jlcjak/astra_piNas/docs/images/render-bottom.png

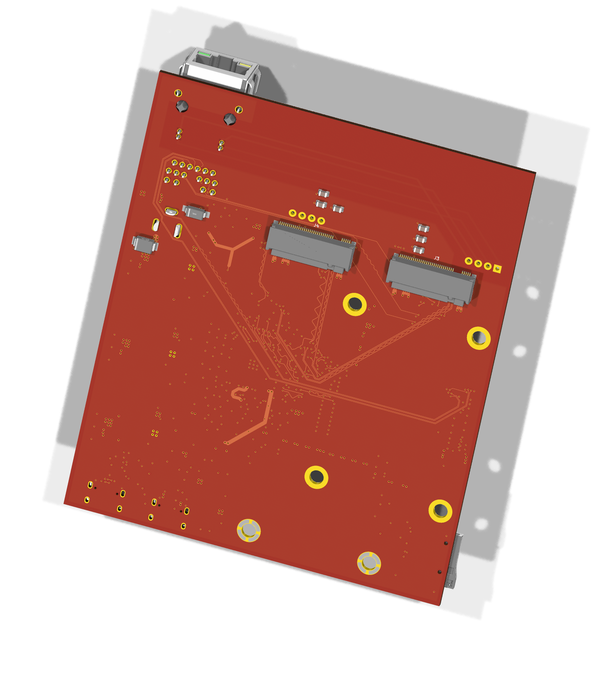
docs/images/render-bottom.png
