jlcjak/astra_piNas/docs/images/render-top.png

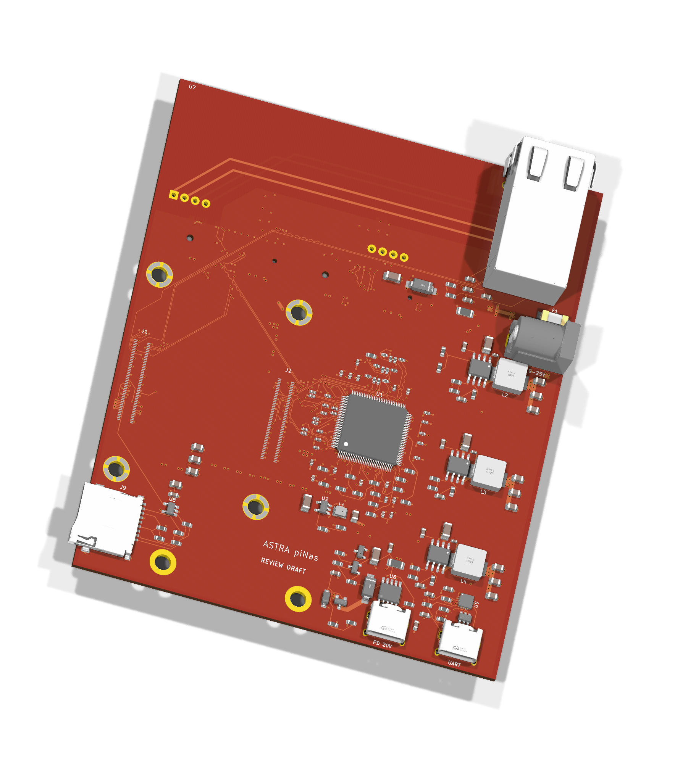
docs/images/render-top.png
