jlcjak/astra_piNas/docs/inputs_review.png

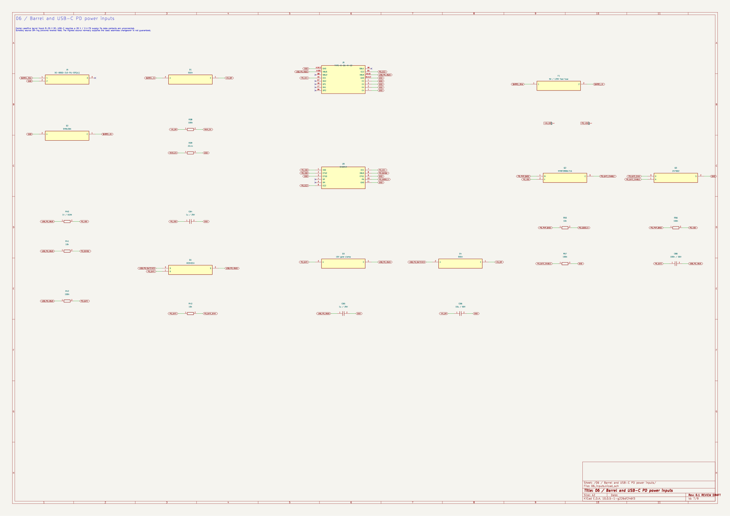
docs/inputs_review.png
