jlcjak/astra_piNas/docs/pcie_review.png

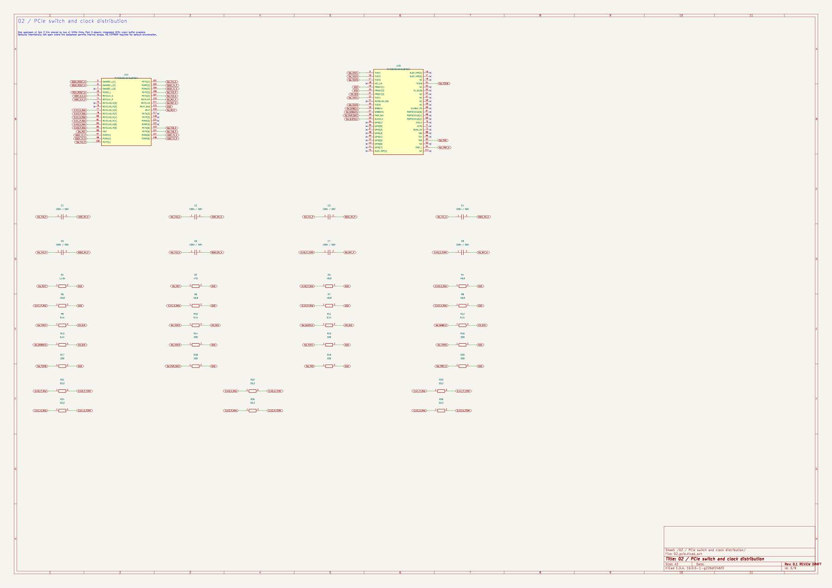
docs/pcie_review.png
