jlcjak/astra_piNas/sources/barrel_reference.png

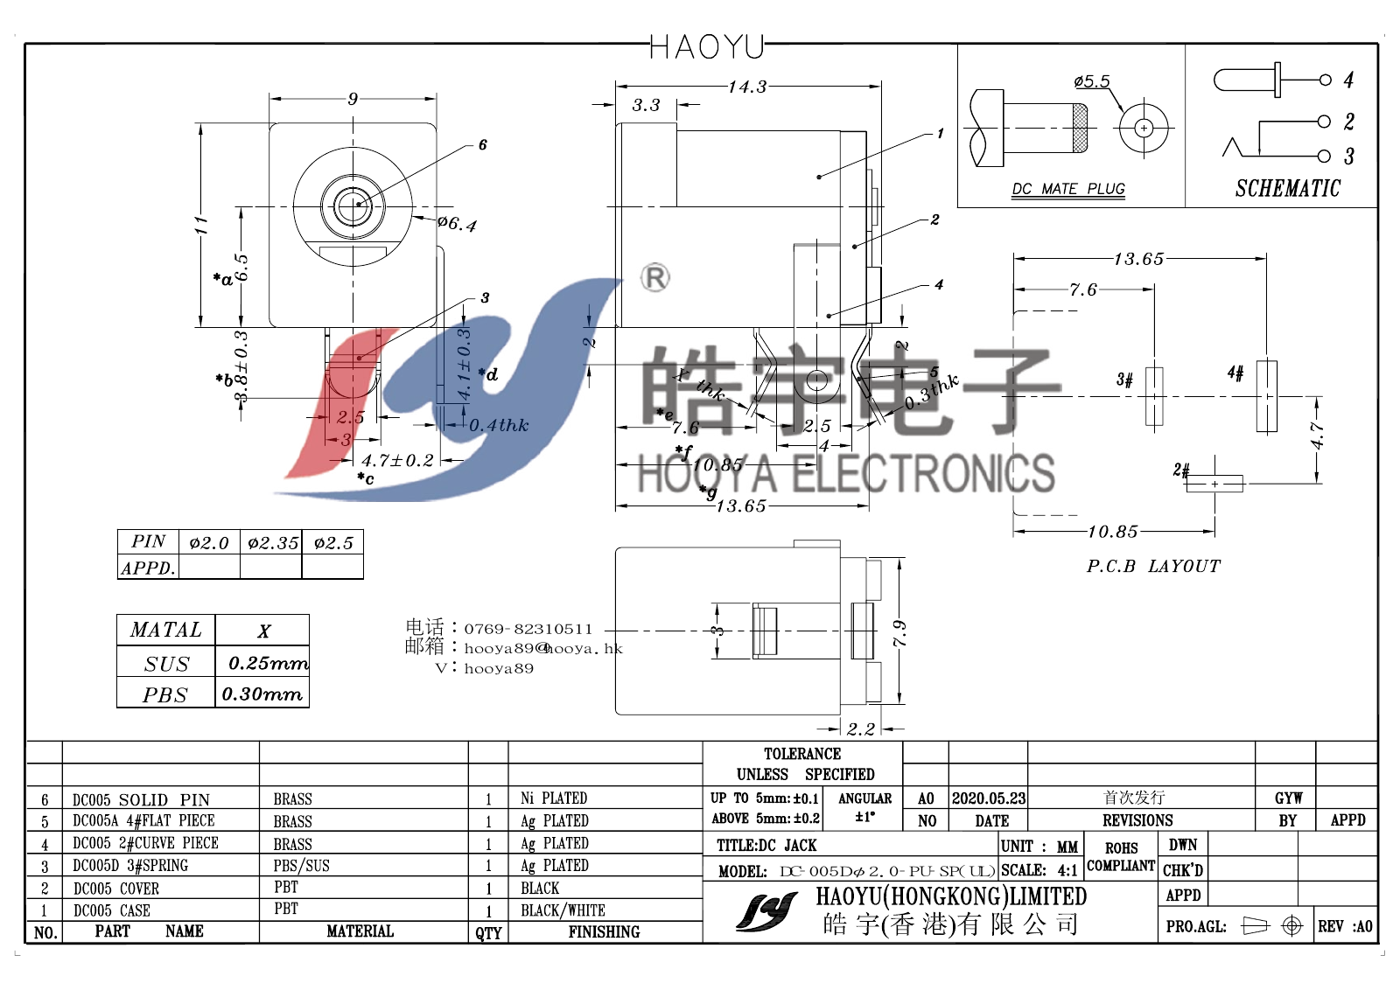
sources/barrel_reference.png
