jlcjak/astra_piNas/sources/cm_land.png

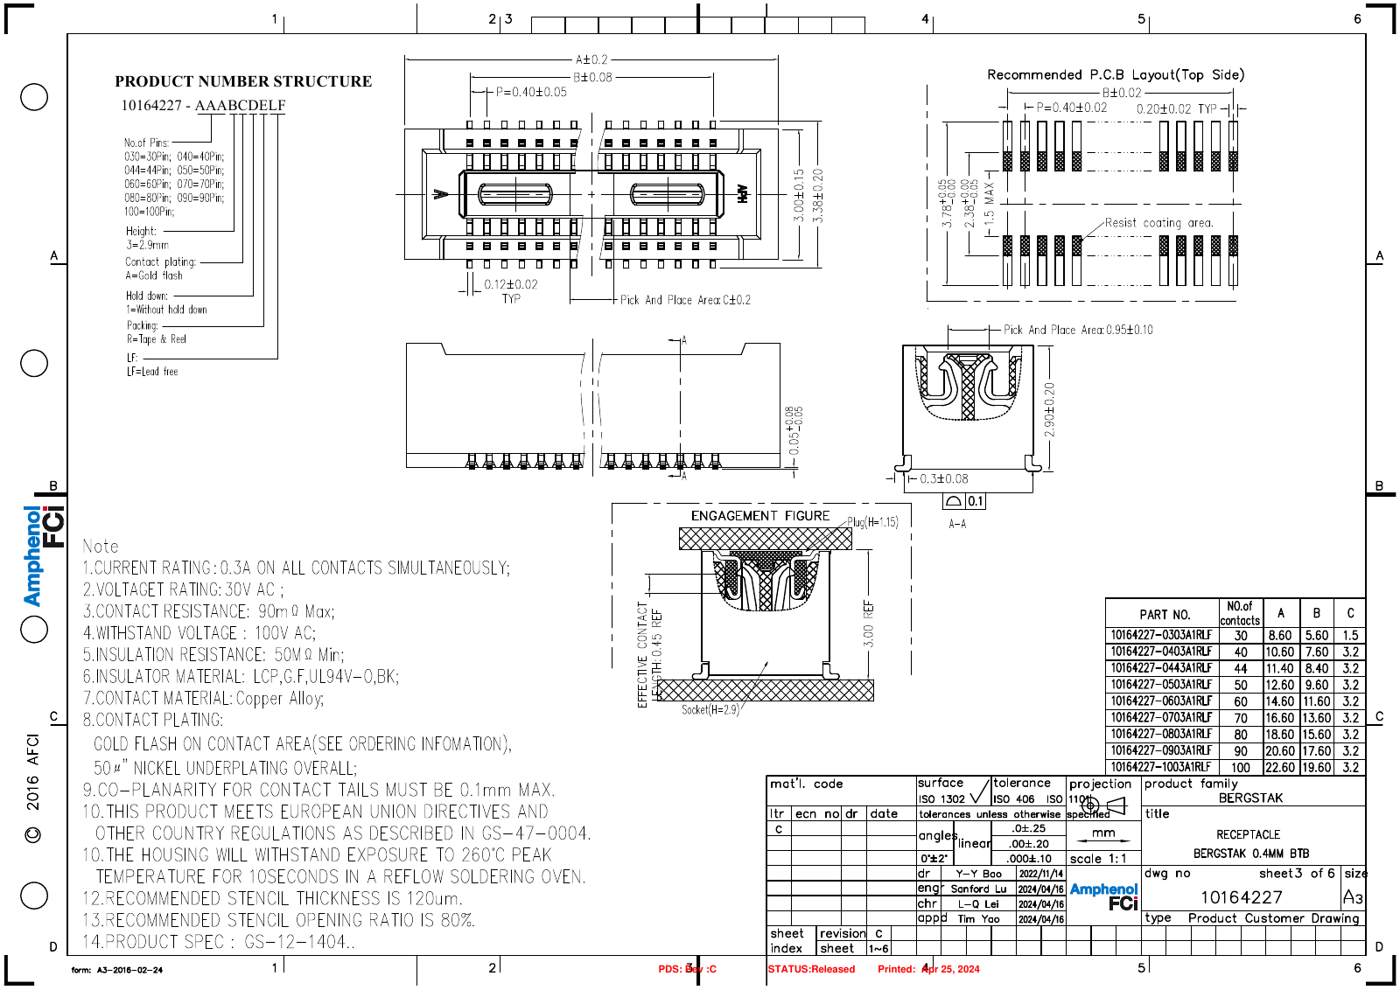
sources/cm_land.png
