jlcjak/astra_piNas/sources/m2_body.png

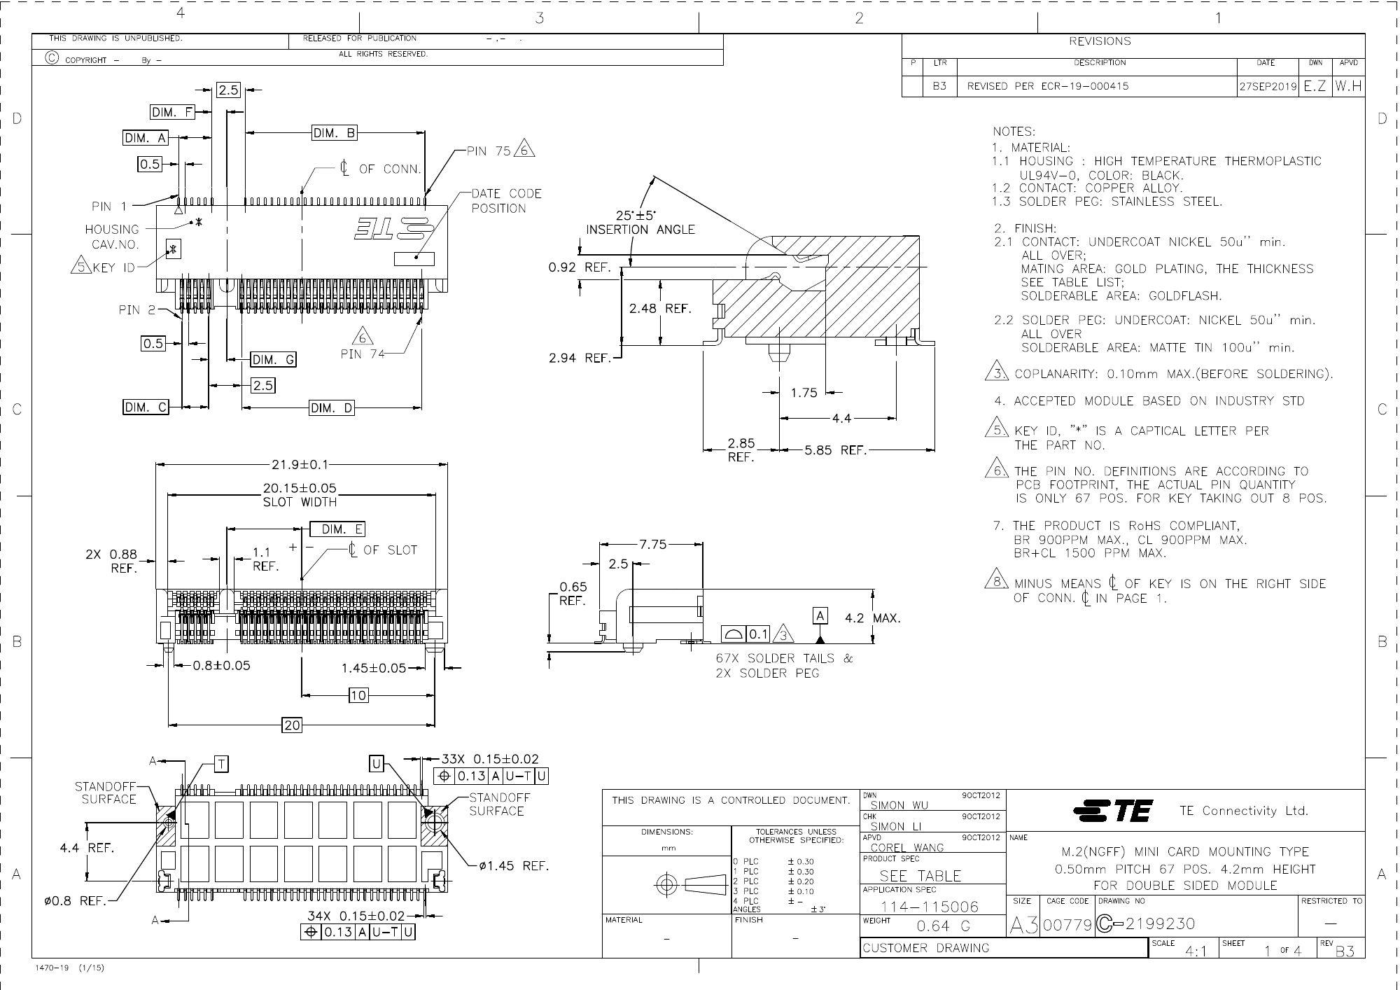
sources/m2_body.png
