jlcjak/astra_piNas/sources/m2_drawing.png

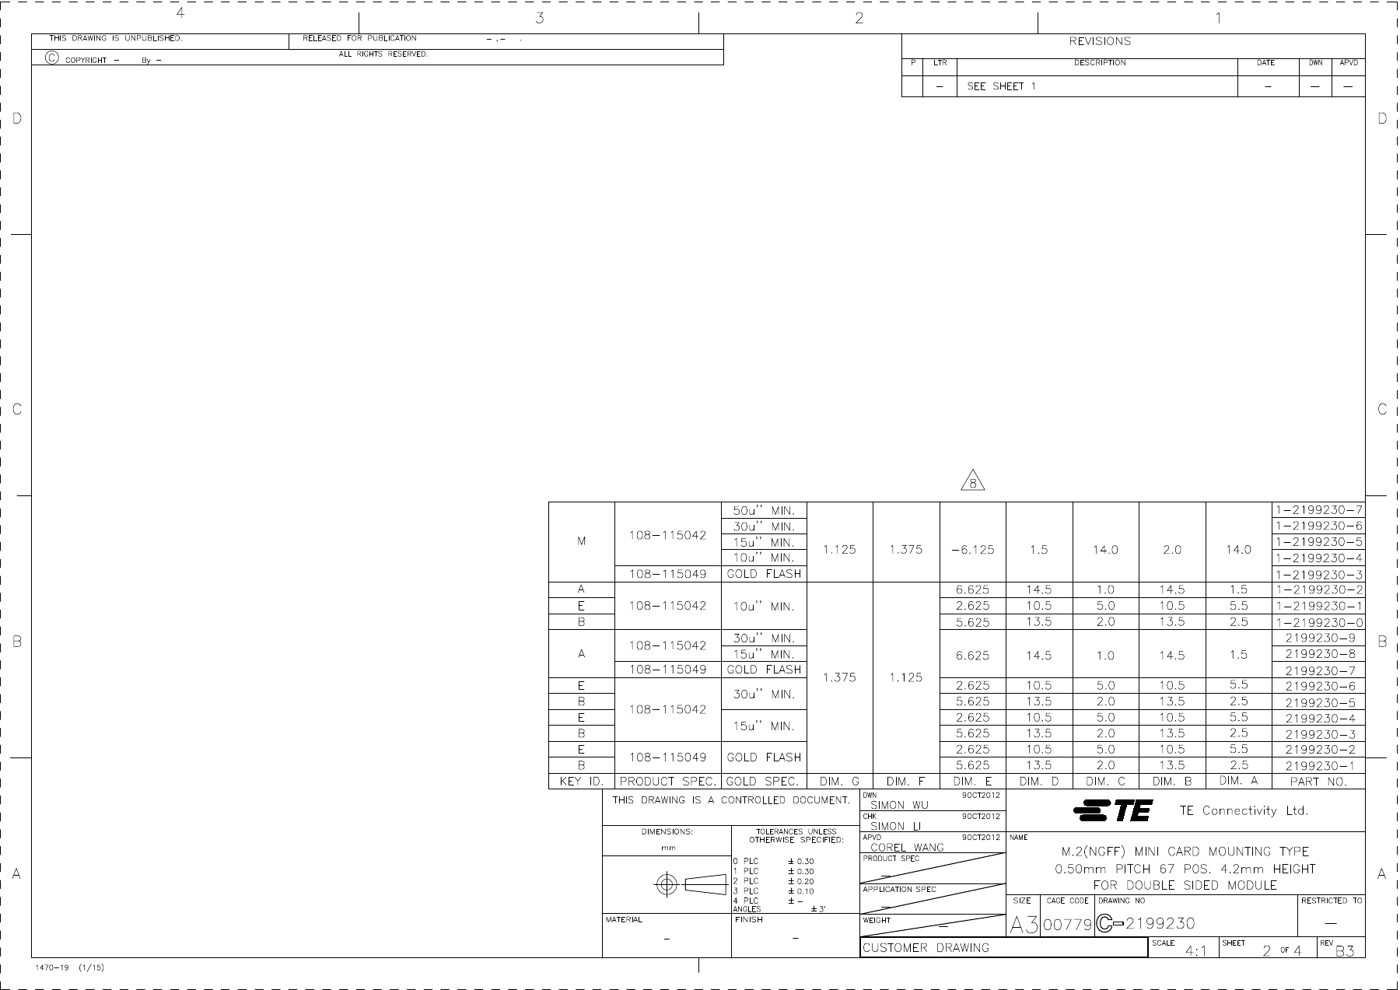
sources/m2_drawing.png
