jlcjak/astra_piNas/sources/m2_land.png

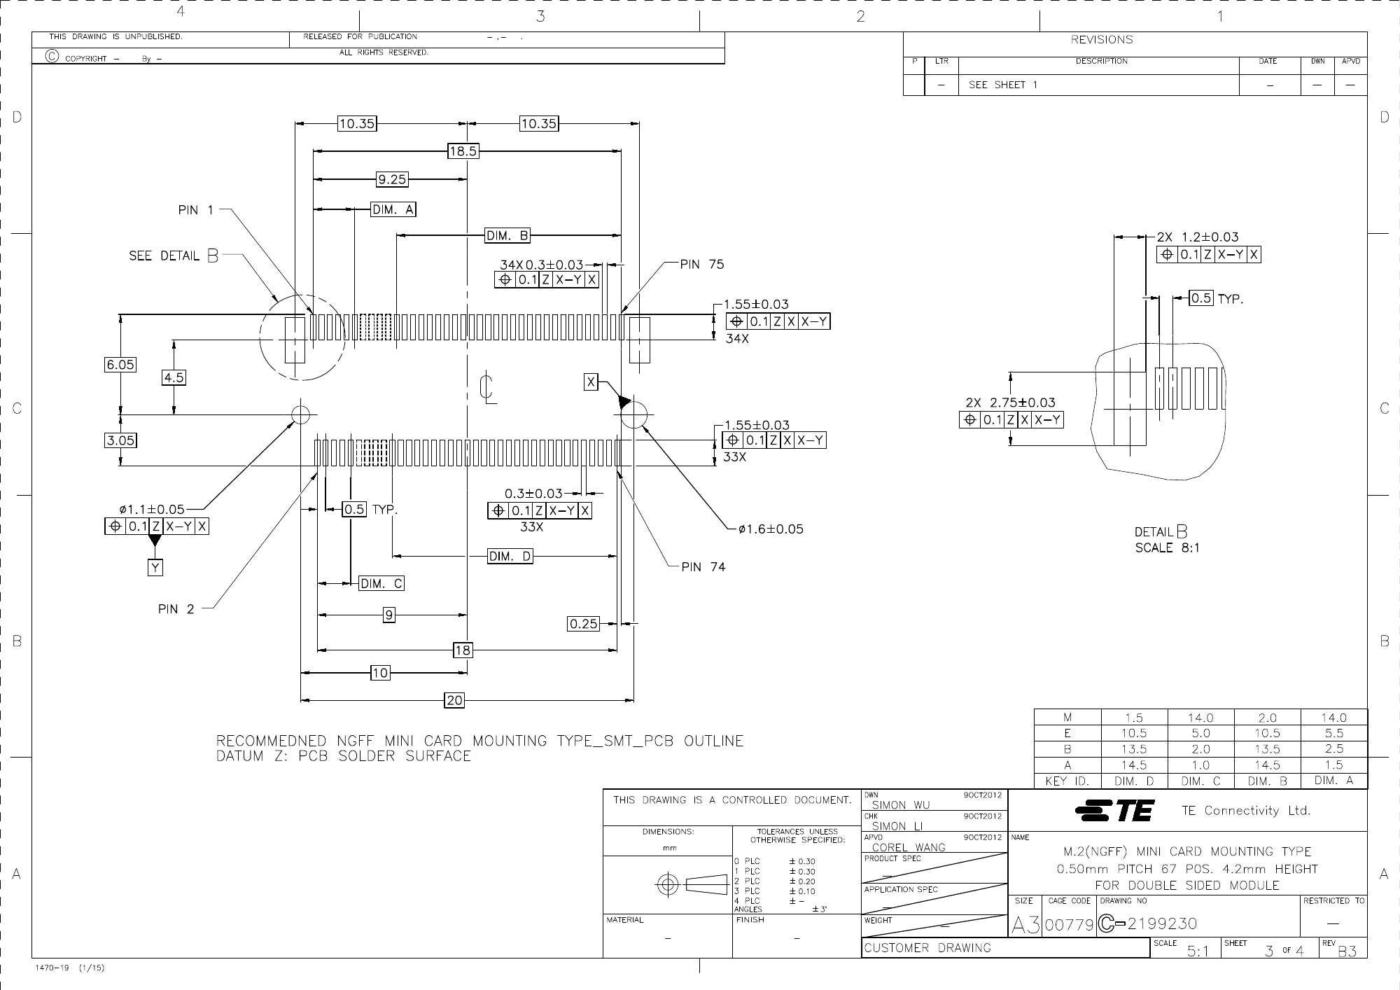
sources/m2_land.png
