jlcjak/astra_piNas/sources/m2_mount.png

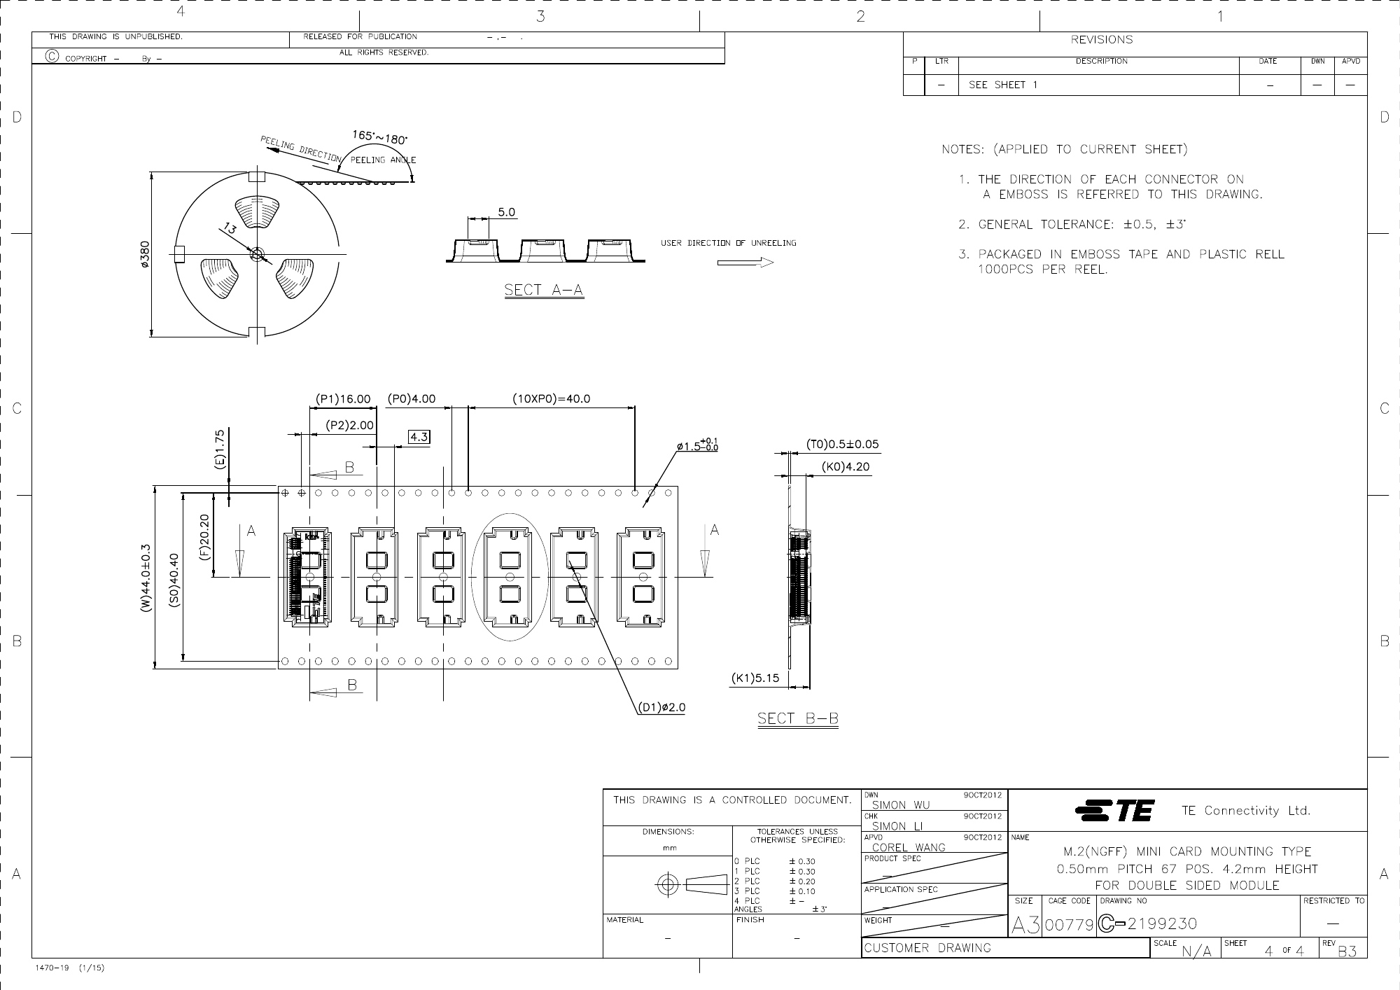
sources/m2_mount.png
