jlcjak/astra_piNas/sources/magjack_circuit.png

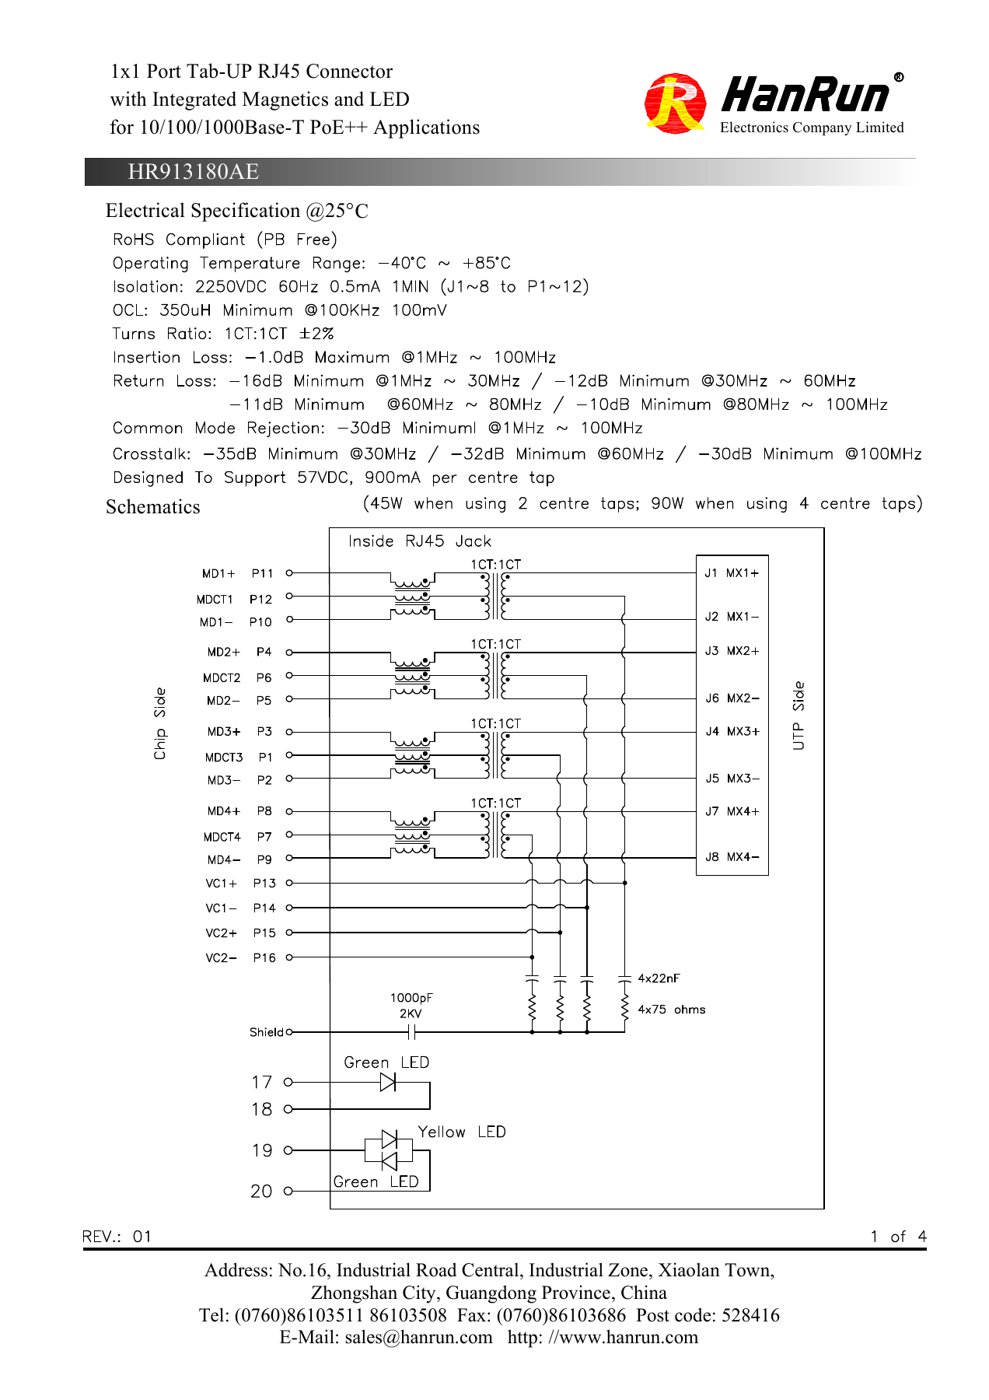
sources/magjack_circuit.png
