jlcjak/astra_piNas/sources/magjack_diagram.png

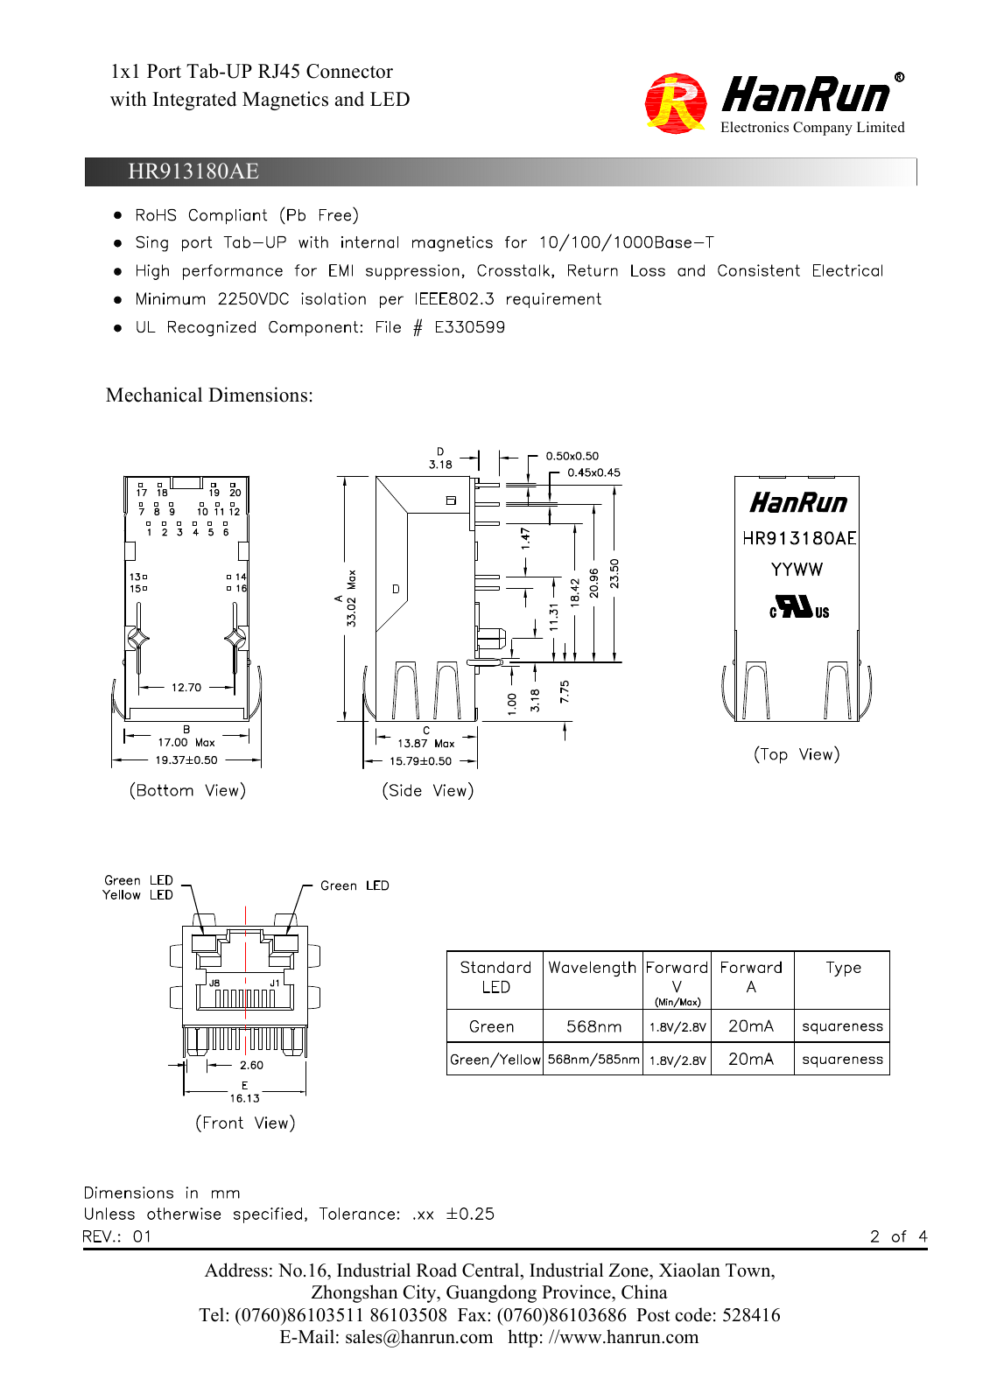
sources/magjack_diagram.png
