jlcjak/astra_piNas/sources/pd_reference.png

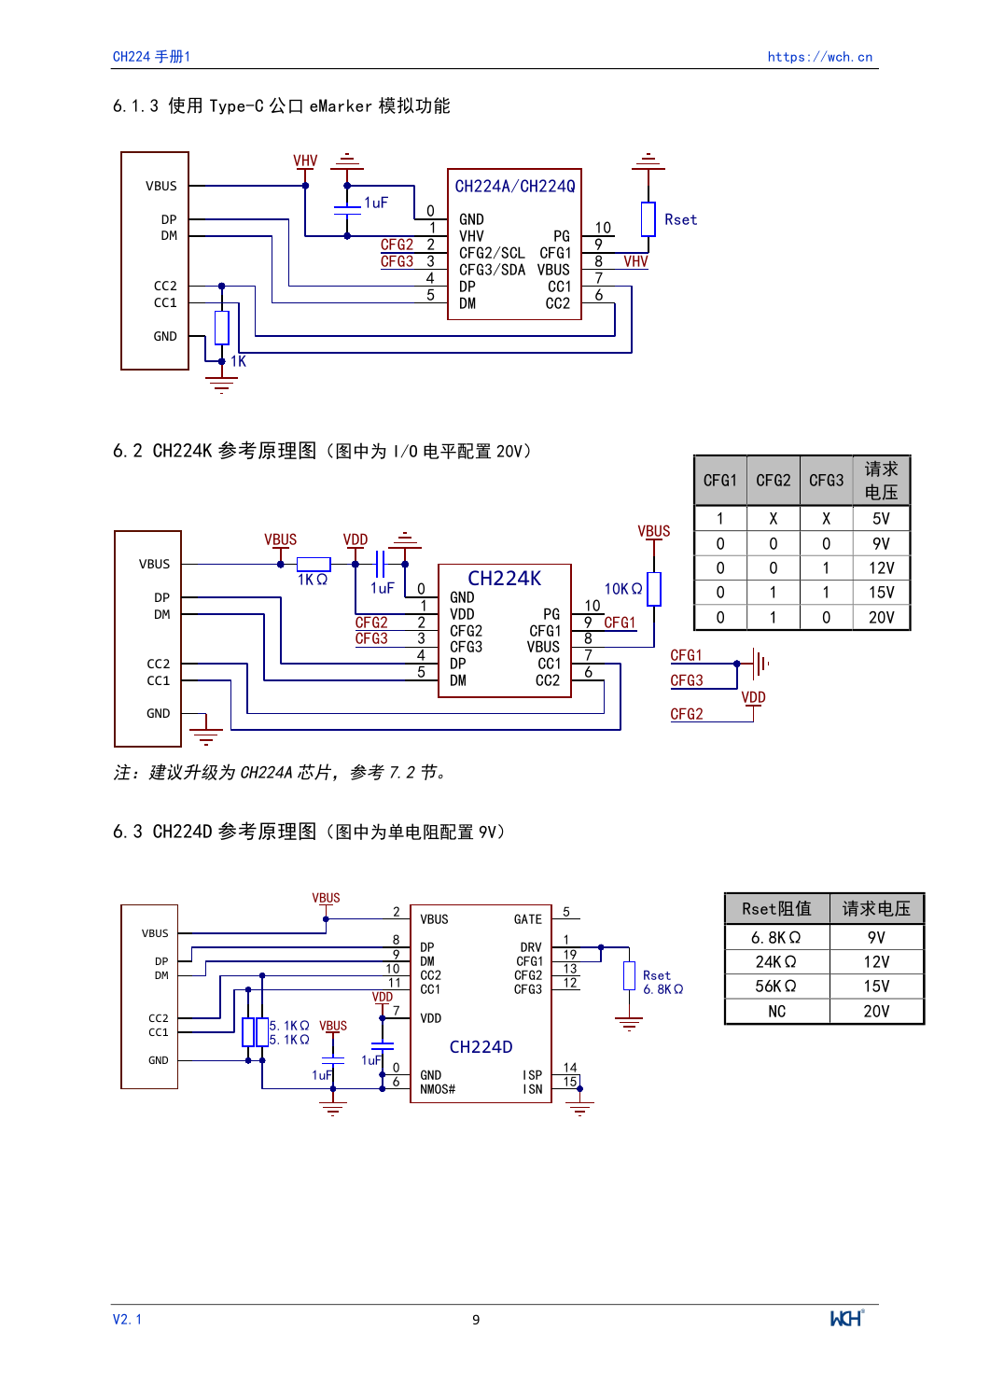
sources/pd_reference.png
