jlcjak/astra_piNas/sources/standoff.png

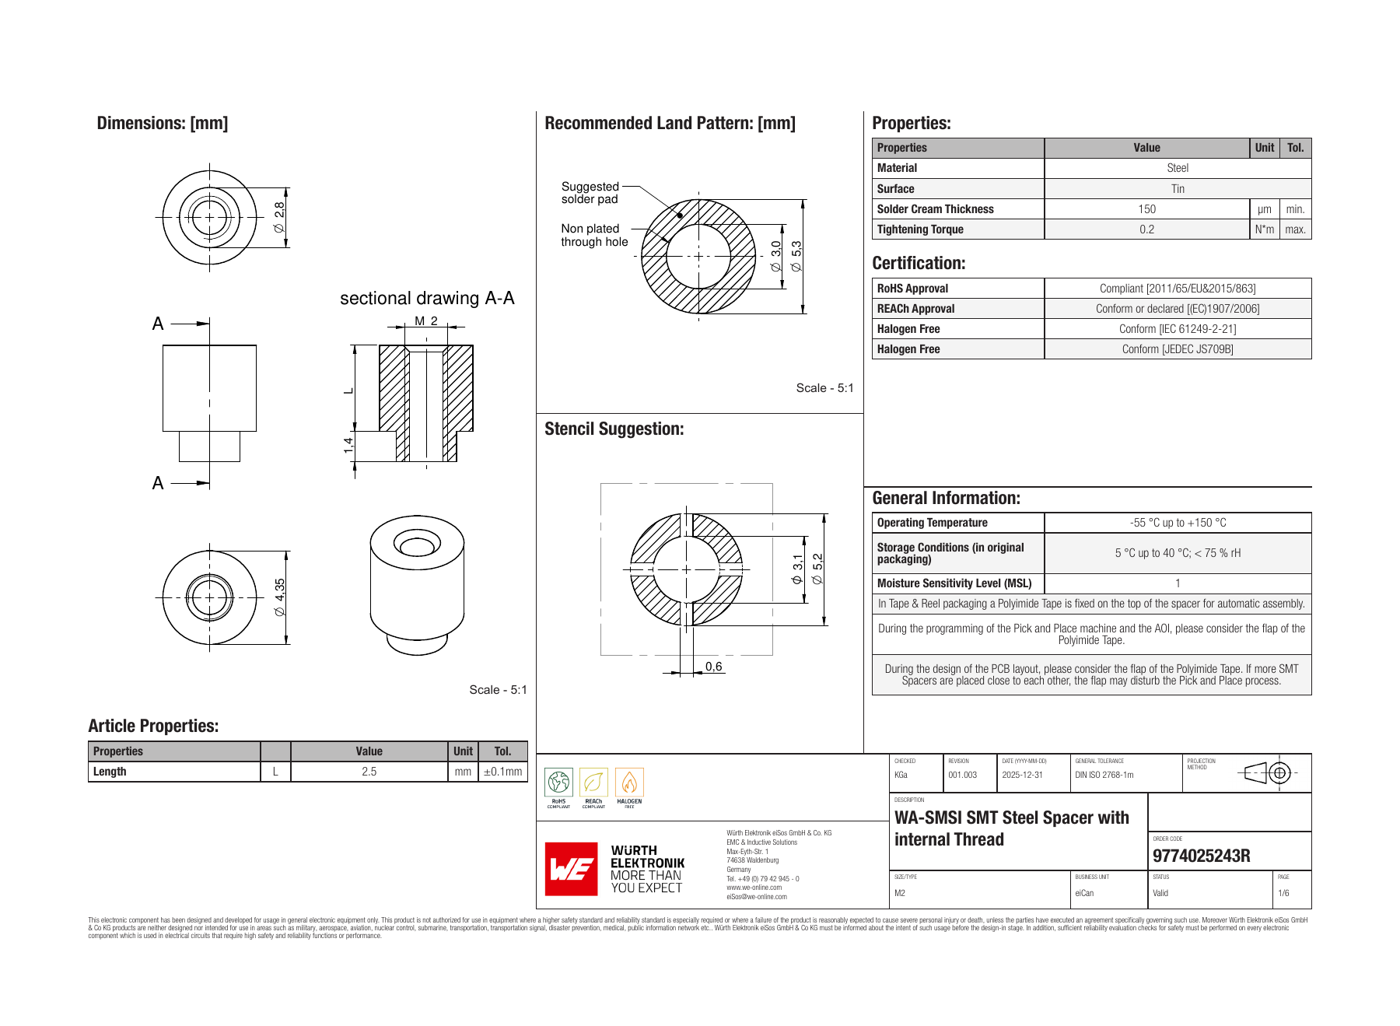
sources/standoff.png
