jlcjak/astra_piNas/sources/yiyuan.png

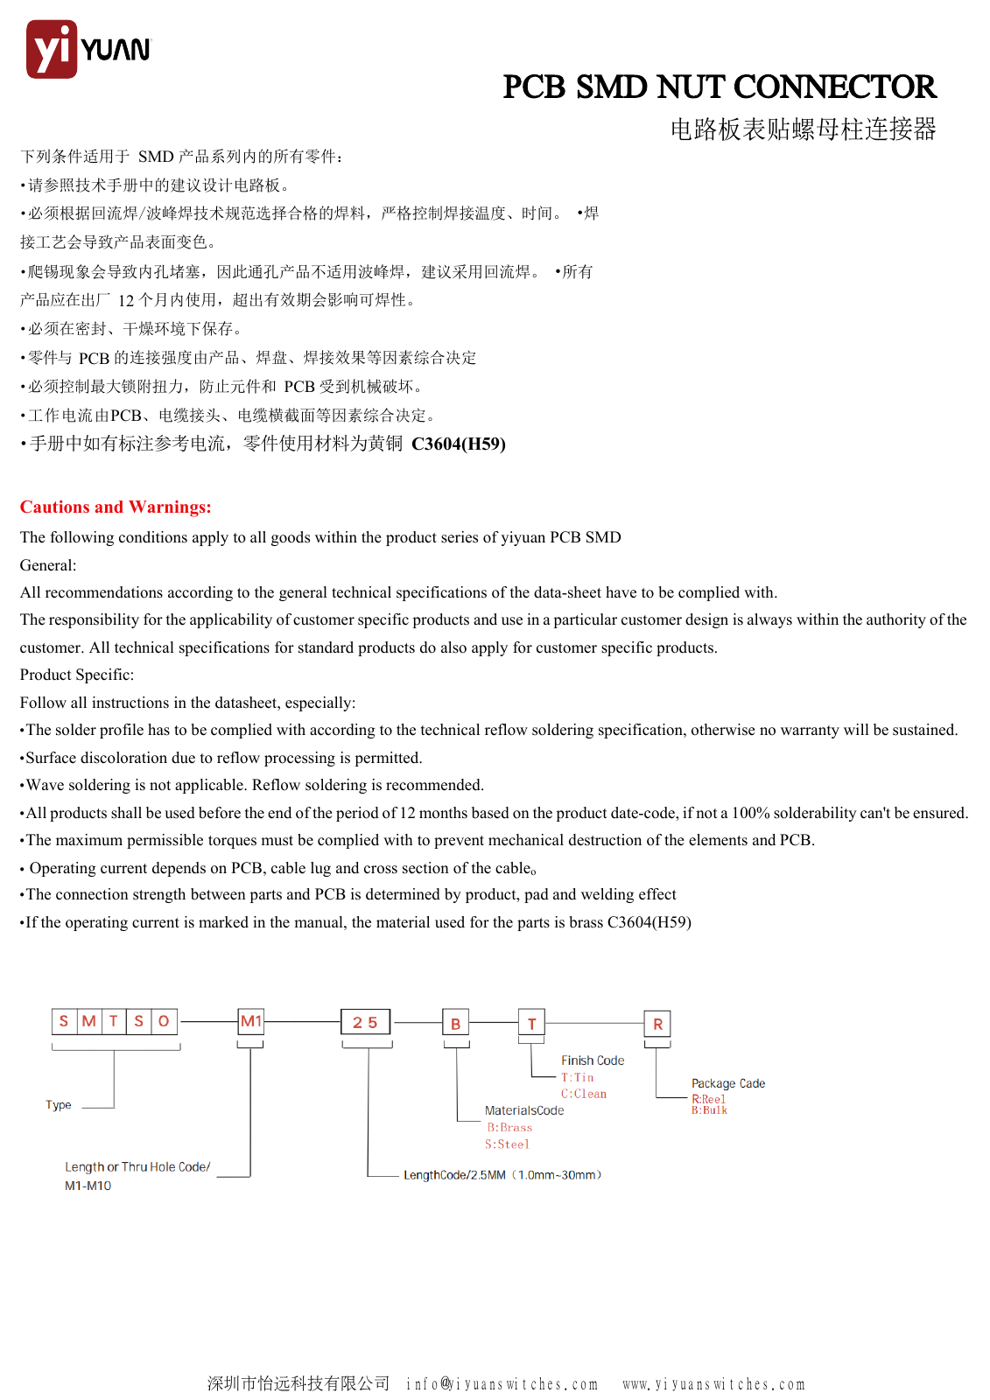
sources/yiyuan.png
