jlcjak/astra_piNas/sources/yiyuan_dims.png

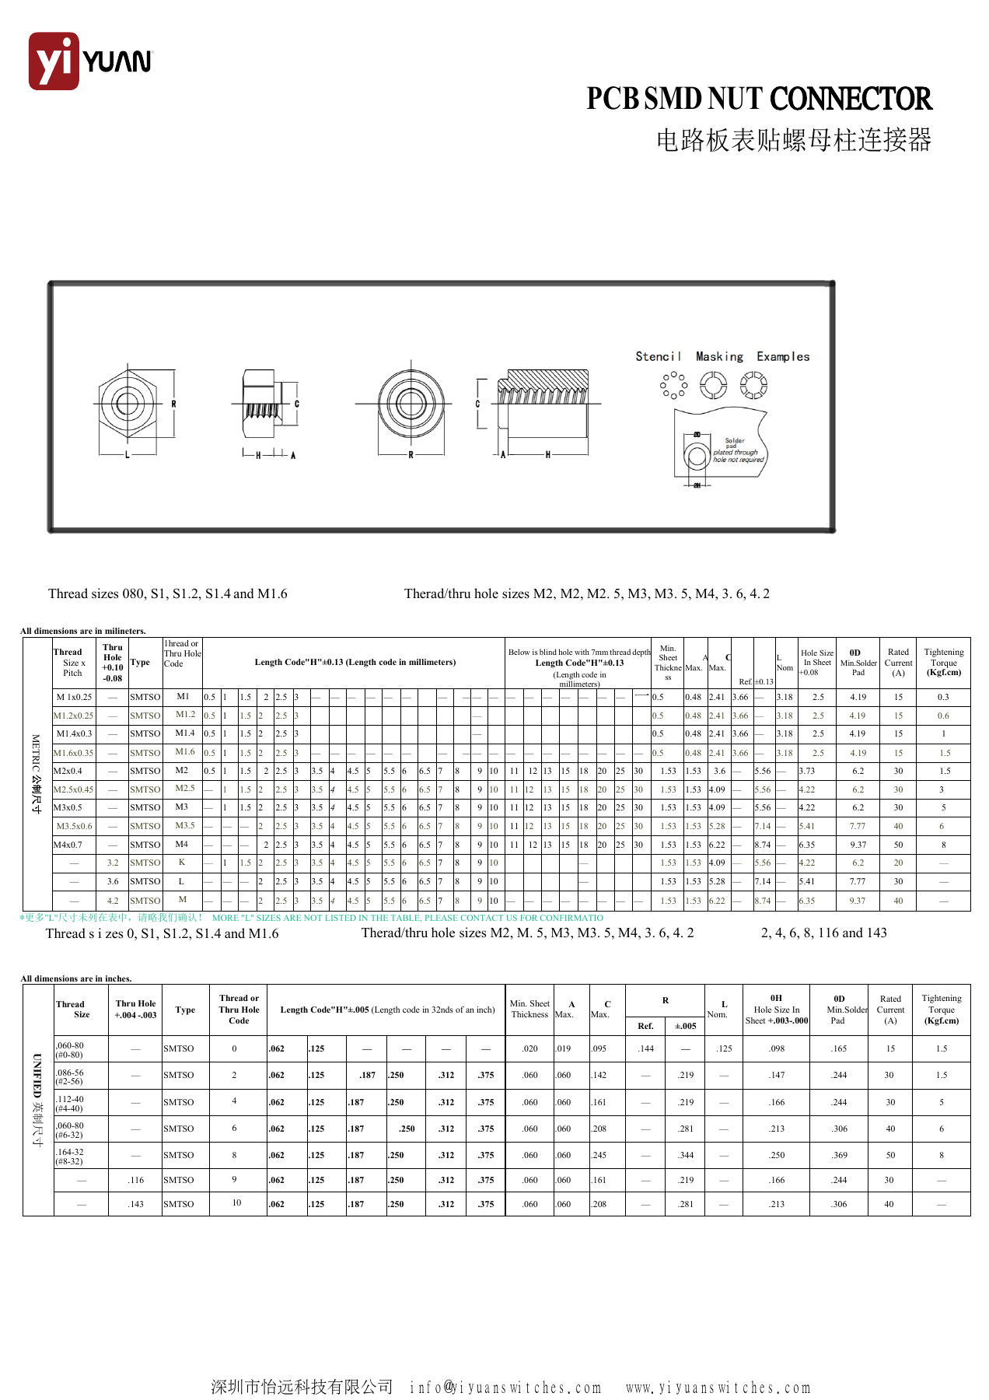
sources/yiyuan_dims.png
