jlcjak/astra_piNas/docs/qa_2.png

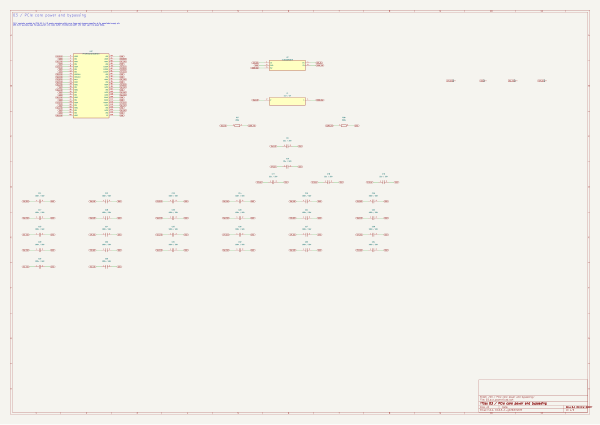
docs/qa_2.png
